michaelmangelsdorf/Sonne8/Prototype/verilog/sasm.c

/* Sonne Microcontroller rev. Myth
    Assembler
  Jan-2024 Michael Mangelsdorf
  Copyr. <mim@ok-schalter.de>
 */

#include <stdio.h>
#include <stdlib.h>
#include <string.h>
#include <ctype.h>

#define LHS_N     0
#define LHS_M     1
#define LHS_D     2
#define LHS_O     3
#define LHS_R     4
#define LHS_I     5
#define LHS_S     6
#define LHS_P     7

#define RHS_G     0
#define RHS_M     1
#define RHS_D     2
#define RHS_O     3
#define RHS_R     4
#define RHS_I     5
#define RHS_S     6
#define RHS_P     7
#define RHS_E     8
#define RHS_X     9
#define RHS_J     10
#define RHS_T     11
#define RHS_F     12
#define RHS_C     13
#define RHS_A     14
#define RHS_B     15

struct myth_vm {

    uint8_t reg_G;
    uint8_t reg_D;
    uint8_t reg_O;
    uint8_t reg_R;
    uint8_t reg_I;
    uint8_t reg_A;
    uint8_t reg_B;
    uint8_t reg_LJO;
    uint8_t reg_C;
    uint8_t reg_L;
    uint8_t reg_E;
    uint8_t reg_SIR;
    uint8_t reg_SOR;
    uint8_t reg_PIR;
    uint8_t reg_POR;
    uint8_t reg_PC;
    uint8_t reg_xMx;

    uint8_t par_ready;
    uint8_t ser_clock;

    uint8_t pagebuf[256];
    uint8_t ram[0x8000];
    
    struct {
        char name[13];
        uint8_t page_idx;
        uint8_t byte_idx;
        uint8_t value;
    } labels;

    void (*E_posedge[16])(struct myth_vm*);
    void (*E_negedge[16])(struct myth_vm*);
} vm;


unsigned pass; /* counts assembly passes */

/* Generate a table of all possible instruction mnemonics */
/* Array index equates to operation code */

char mnemo_decoder[256][12]; /* Various formats */


char *rhs[] = {
"G", "M", "D", "O",
"R", "I", "S", "P",
"E", "X", "J", "T",
"F", "C", "A", "B"
};

void gen_opcodes()
{
    char *lhs[] = {
     "N", "M", "D", "O",
     "R", "I", "S", "P" 
    };

    char *sys[] = {
     "NOP", "SSI", "SSO", "SCL", "SCH", "RDY", "NEW", "OLD",
     "P4", "P1", "P2", "P3", "M4", "M3", "M2", "M1"
    };

    char *aluop[] = {
     "IDA", "IDB", "OCA", "OCB",
     "SLA", "SLB", "SRA", "SRB",
     "AND", "IOR", "EOR", "ADD",
     "CAR", "ALB", "AEB", "AGB"
    };

    char numstr[] = "0";




    // SYS instructions (16 opcodes, 0-15)
    for (int i=0; i<16; i++) {
        strcpy(mnemo_decoder[i], sys[i]);
    }

    // ALU instructions (16 opcodes, 16-31)
    for (int i=16; i<32; i++) {
        strcpy( mnemo_decoder[i], aluop[i-16]);
    }

    // TRAP instructions (32 opcodes, 32-63)
    for (int i=32; i<64; i++) {
        sprintf(mnemo_decoder[i], "*%d", i-32);
    }

    // GETPUT instructions (64 opcodes, 64-127)      
    for (int offs=0; offs<4; offs++)
      for (int regn=0; regn<4; regn++)
        for (int gp=0; gp<2; gp++)
            for (int gl=0; gl<2; gl++)
                {
                    numstr[0] = 48 + offs; // ASCII 0 + the number
                    unsigned index = 64 + regn + 4*gl + 8*gp + 16*offs;
                    if (gp==0) { // GET
                        strcpy( mnemo_decoder[index], gl==0 ? "G" : "L");
                        strcat( mnemo_decoder[index], numstr);
                       switch (regn) {
                        case 0: strcat( mnemo_decoder[index], "a"); break;
                        case 1: strcat( mnemo_decoder[index], "b"); break;
                        case 2: strcat( mnemo_decoder[index], "r"); break;
                        case 3: strcat( mnemo_decoder[index], "i"); break;
                        }
                    }
                    else { // PUT
                       switch (regn) {
                        case 0: strcpy( mnemo_decoder[index], "a"); break;
                        case 1: strcat( mnemo_decoder[index], "b"); break;
                        case 2: strcat( mnemo_decoder[index], "r"); break;
                        case 3: strcat( mnemo_decoder[index], "i"); break;
                        }
                        strcat( mnemo_decoder[index], gl==0 ? "G" : "L");
                        strcat( mnemo_decoder[index], numstr);
                    }
                }


    // PAIR 128-255
    for (int j=0; j<8; j++)
    {
           for (int i=0; i<16; i++)
           {
             /*scrounge*/
           if (j==LHS_N && i==RHS_M) strcpy( mnemo_decoder[j*16+i + 128], "RET");
           else if (j==LHS_D && i==RHS_C) strcpy( mnemo_decoder[j*16+i + 128], "LJO");
           else if(j==LHS_O && i==RHS_C) strcpy( mnemo_decoder[j*16+i + 128], "CPI");
           else if(j==LHS_M && i==RHS_M) strcpy( mnemo_decoder[j*16+i + 128], "CLR");
           else {     
                /* Transfers */
                strcpy( mnemo_decoder[j*16+i + 128], lhs[j] );
//                if (j==RHS_B || j==RHS_BR || j==RHS_BRZ || j==RHS_BT) {
//                    strcat( mnemo_decoder[i*16+j], "'");
//                }
                strcat( mnemo_decoder[j*16+i + 128], rhs[i]);
                //printf("%s %d %d\n", mnemo_decoder[j*16+i], j*16, i);
            }
          }
    }

}




#define SYMSIZE 26

/* Provide a table for frame mnemonics */

char frame_mnemo[256][16][SYMSIZE];
uint8_t frame_refs[256][16];
uint8_t offslabels;
uint8_t frame_lid[256]; /* #Bytes defined in each frame */
uint8_t frame_mnemo_export[256]; /* Non-zero value: export */

uint8_t theDamned;

/* Generate a dictionary for number names */

struct {
    char name[SYMSIZE];
    uint8_t val;
    uint8_t frame;
    int type; // bit map, bit 0=export
} defmap[8192];
unsigned defmap_topindex;

#define BYTE_TO_BINARY_PATTERN "%c%c%c%c_%c%c%c%c"
#define BYTE_TO_BINARY(byte)  \
  (byte & 0x80 ? '1' : '0'), \
  (byte & 0x40 ? '1' : '0'), \
  (byte & 0x20 ? '1' : '0'), \
  (byte & 0x10 ? '1' : '0'), \
  (byte & 0x08 ? '1' : '0'), \
  (byte & 0x04 ? '1' : '0'), \
  (byte & 0x02 ? '1' : '0'), \
  (byte & 0x01 ? '1' : '0') 

#define NYBBLE_TO_BINARY_PATTERN "%c%c%c%c"
#define NYBBLE_TO_BINARY(nybble)  \
  (nybble & 0x08 ? '1' : '0'), \
  (nybble & 0x04 ? '1' : '0'), \
  (nybble & 0x02 ? '1' : '0'), \
  (nybble & 0x01 ? '1' : '0') \

    void create_def( char* label, uint8_t val) {
            sprintf(defmap[defmap_topindex].name, "%s", label);
            defmap[defmap_topindex].val = val;
            defmap_topindex++;
    }

    void populate_defmap()
    {
        defmap_topindex = 0;
        /* Create decimal numbers */
        for (int i=0; i<256; i++) {
            sprintf(defmap[defmap_topindex].name, "%d", i);
            defmap[defmap_topindex].val = i;
            defmap_topindex++;
        }

        /* Create negative decimals */
        for (int i=1; i<=128; i++) {
            sprintf(defmap[defmap_topindex].name, "-%d", i);
            defmap[defmap_topindex].val = -i & 0xFF;
            defmap_topindex++;
        }

        /* Create zero-padded hex numbers */
        for (int i=0; i<256; i++) {
            sprintf(defmap[defmap_topindex].name, "%02X", i);
            strcat(defmap[defmap_topindex].name, "h");
            defmap[defmap_topindex].val = i;
            defmap_topindex++;
        }
        /* Create unpadded hex numbers (nybbles) */
        for (int i=0; i<16; i++) {
            sprintf(defmap[defmap_topindex].name, "%X", i);
            strcat(defmap[defmap_topindex].name, "h");
            defmap[defmap_topindex].val = i;
            defmap_topindex++;
        }
        /* Create binary numbers byte */
        for (int i=0; i<256; i++) {
            sprintf(defmap[defmap_topindex].name, BYTE_TO_BINARY_PATTERN, BYTE_TO_BINARY(i));
            strcat(defmap[defmap_topindex].name, "b");
            defmap[defmap_topindex].val = i;
            defmap_topindex++;
        }
        /* Create binary numbers nybble */
        for (int i=0; i<16; i++) {
            sprintf(defmap[defmap_topindex].name, NYBBLE_TO_BINARY_PATTERN, NYBBLE_TO_BINARY(i));
            strcat(defmap[defmap_topindex].name, "b");
            defmap[defmap_topindex].val = i;
            defmap_topindex++;
        }

        /* Create ASCII names and others */

        create_def("ASCII.backspace", 8);
        create_def("ASCII.linefeed", 10);
        create_def("ASCII.escape", 27);
        create_def("ASCII.space", 32);
        create_def("ASCII.exclamation_mark", 33);
        create_def("ASCII.double_quote", 34);
        create_def("ASCII.hashmark", 35);
        create_def("ASCII.dollar", 36);
        create_def("ASCII.percent", 37);
        create_def("ASCII.ampersand", 38);
        create_def("ASCII.single_quote", 39);
        create_def("ASCII.opening_parenthesis", 40);
        create_def("ASCII.closing_parenthesis", 41);
        create_def("ASCII.asterisk", 42);
        create_def("ASCII.plus_sign", 43);
        create_def("ASCII.comma", 44);
        create_def("ASCII.minus_sign", 45);
        create_def("ASCII.full_stop", 46);
        create_def("ASCII.forward_slash", 47);
        
        // ASCII 0-9 48-57

        create_def("ASCII.colon", 58);
        create_def("ASCII.semicolon", 59);
        create_def("ASCII.less_than_sign", 60);
        create_def("ASCII.equal_sign", 61);
        create_def("ASCII.greater_than_sign", 62);
        create_def("ASCII.question_mark", 63);
        create_def("ASCII.at_sign", 64);

        // ASCII A-Z 65-90

        create_def("ASCII.opening_bracket", 91);
        create_def("ASCII.backward_slash", 92);
        create_def("ASCII.closing_bracket", 93);
        create_def("ASCII.caret", 94);
        create_def("ASCII.underscore", 95);
        create_def("ASCII.back_tick", 96);

        // ASCII a-z 97-122

        create_def("ASCII.opening_brace", 123);
        create_def("ASCII.pipe_symbol", 124);
        create_def("ASCII.closing_brace", 125);
        create_def("ASCII.tilde", 126);
        
        create_def("ASCII.del", 127);

        // Create GLOBAL variable names

        create_def("G0", 128);
        create_def("G1", 129);
        create_def("G2", 130);
        create_def("G3", 131);
        create_def("G4", 132);
        create_def("G5", 133);
        create_def("G6", 134);
        create_def("G7", 135);

        // Create LOCAL variable names

        create_def("L0", 192);
        create_def("L1", 193);
        create_def("L2", 194);
        create_def("L3", 195);
        create_def("L4", 196);
        create_def("L5", 197);
        create_def("L6", 198);
        create_def("L7", 199);


    }




char wordbuf[SYMSIZE];
char tempbuf[SYMSIZE];
char *src; /* Will point to in-memory copy of source file */
long srclength; /* Number of bytes in src file */

/*  Read source file into a memory buffer */

    char* readsrcf( const char* fname)
    {
        FILE* f = fopen( fname,"rb");
        if (!f) return NULL;

        fseek( f, 0, SEEK_END);
        srclength = ftell( f) + 1;
        fseek( f, 0, SEEK_SET);

        char *buffer = malloc (srclength);
        if (buffer) {
          fread (buffer, 1, srclength-1, f);
          buffer[srclength]='\0';
        }
        fclose( f);
        return buffer;
    }

uint8_t isinram = 0;

//uint8_t vm.ram[256*128]; /* 128 (ROM only) frames * 128 bytes = 32k */
unsigned ROM_srcLine[256*128]; /* Which line number generated the output byte */

unsigned objcursor; /* holds current object code byte index */
unsigned objframe; /* hold highest object code frame index */

/* Clear structures */

    void clear()
    {
        for (int i=0; i<(256*128); i++) vm.ram[i] = 0;

        for (int i=0; i<256; i++) 
            strcpy(frame_mnemo[i][offslabels],"");

    }

unsigned cursor; /* holds current source text character index */
unsigned lines; /* tracks number of lines processed */

/* Get a source character relative relative to current position */

    int nextchar( int displacement){
        unsigned index = cursor + displacement;
        if (index < srclength) return src[index];
        else return 0;
    }

/* Move text cursor forward if not outside source buffer */

    int cursor_fwd( int displacement){
    	unsigned index = cursor + displacement;
    	if (index >= srclength) return -1;
    	else cursor = index;
    	return 0;
    }

/* Skip the rest of the current line, including any number of trailing
 * line breaks.
 */

    int skipline(){
    	while (src[cursor]!='\n')
    		if (cursor_fwd(1)) return -1;
    	return 0;
    }

/* Skip any number of space characters */

    int skipspace(){
    	while (src[cursor]==' ' || src[cursor]=='\t')
    		if (cursor_fwd(1)) return -1;
    	return 0;
    }


/* Validate label references */

    int find_backref(char* refstr)
    {
        //printf("BACKW REFSTR=%s\n", refstr);
        unsigned here;
            here = objframe;
            for (int i=here; i>=0; i--) {
                for(int j=0; j<16; j++)
                    if (!strcmp(refstr, frame_mnemo[i][j])) {
                        theDamned = i;
                        return frame_refs[i][j];
                    }
            }
        return -1;
    }

    int find_fwdref(char* refstr)
    {
        //printf("FWD REFSTR=%s\n", refstr);
        unsigned here;
            here = objframe;
            for (int i=here; i<256; i++) {
                for(int j=0; j<16; j++) {
                    //if (!strcmp(refstr, "skip") && i<4)
                    //    printf("i=%d, j=%d, %s, searching for:%s %d\n", i,j, frame_mnemo[i][j], refstr, frame_refs[i][j]);
                    if (!strcmp(refstr, frame_mnemo[i][j])) {
                        theDamned = i;
                        return frame_refs[i][j];
                    }
                }
            }
        return -1;
    }

    int find_mcref(char* refstr)
    {
        //printf("FWD REFSTR=%s\n", refstr);
        unsigned here;
        for (int i=0; i<256; i++)
            for(int j=0; j<16; j++)
                if (!strcmp(refstr, frame_mnemo[i][j])) return i;
        return -1;
    }




/* Try to find the frame and the type of a defmap entry */

    int defmap_frame_and_type(char* buf, uint8_t* typefound)
    {
        for (int i=0; i<defmap_topindex; i++)
        {
            if (!strcmp( defmap[i].name, buf)) {
                //printf ("Found def %s\n", wordbuf);
                *typefound = defmap[i].type;
                return defmap[i].frame;
            }
        }
        return -1;
    }

/* Try to find an entry matching wordbuf in precompiled mnemonics */

    int compare_to_tables(char* buf)
    {
        for (int i=0; i<256; i++)
        {
            if (!strcmp( mnemo_decoder[i], buf)) {
                //printf ("Found mnemonic %s (%02X)\n", wordbuf, i);
                return i;
            }
        }

        for (int i=0; i<defmap_topindex; i++)
        {
            if (!strcmp( defmap[i].name, buf)) {
                //printf ("Found def (or number literal!) %s\n", buf);
                return defmap[i].val;
            }
        }
        return -1;
    }


/* Store an object code byte and move on */

    void store( uint8_t byte)
    {
            ROM_srcLine[objframe * 128 + objcursor] = lines;
            vm.ram[objframe * 128 + objcursor] = byte;
            frame_lid[objframe]++;

        if (++objcursor > 127) {
            printf("Code frame overflow in line %d\n", lines);
            exit(0);
        }
    }


int labelallowed; /* Only one frame label per full-stop */
int endframe;
int handled;
int ramgap;


void
check_if_ref(char* mybuf)
{
    int k;
     if (mybuf[0]=='<') {
        if (strlen(mybuf)<2) {
            printf("Empty back reference, line %d\n** ERROR **\n", lines);
            exit(0);
        }
        k = find_backref(mybuf+1);
        if (theDamned == objframe && k>=objcursor) k=-1; //Handle offset labels
        handled = 1;
    }
    if (mybuf[0]=='>') {
        if (strlen(wordbuf)<2) {
            printf("Empty forward reference, line %d\n** ERROR **\n", lines);
            exit(0);
        }
        k = find_fwdref(mybuf+1);
        if (theDamned == objframe && k<objcursor) k=-1; //Handle offset labels
        //printf("searching for >%s\n",wordbuf+1);
        handled = 1;
    }
    if (handled && k == -1) {
        if (pass==2) {
            printf("Unresolved reference '%s', line %d\n** ERROR **\n", mybuf, lines);
            exit(0);
        }
    }
    if (handled) {
         store(isinram ? k+128 : k);
         //printf("k was %d for %s\n", k, wordbuf);   
    }
}


/* We assert that this is called when cursor is at the first character
 * of a new line, following a line break character.
 * Assemble this line.
 */

    int beginline()
    {
        uint8_t opc_colon;
    	lines++;
        if (src[cursor] == '\n') {
            if (cursor_fwd(1)) return 0; /* skip empty lines */
            else return -1;
        }
        while (skipspace() == 0)  /* Skip leading white space */
        {
            endframe = 0;
            /* We assume that the current word does not end with full-stop */

            handled = 0; /* We haven't handled this word so far */

            /* We are now positioned at the first character of something */
            /* What is it? */

            if (src[cursor] == '\n') { /* It's a newline character, skip it */
                if (cursor_fwd(1)) return 0;
                else return 1; /* Enter next line */
            }
        	
            if (src[cursor] == ';') { /* Beginning of a comment, skip it */
        		if (skipline()) return 0;
                if (cursor_fwd(1)) return 0; /* Skip the newline character */
                else return 1; /* Enter next line */
            }

            /* It's something non-trivial, copy it into the word buffer */
            int k=0;
            while (nextchar(k)!=' ' && nextchar(k)!='\t' && nextchar(k)!='\n')
            {
                wordbuf[k] = nextchar(k);
                if (cursor + k >= srclength) {
                    printf("Unexpected end of file\n");
                    exit(0);
                }
                if (k++ > 79) {
                    printf("Buffer overrun - string literal too long\n");
                    exit(0);
                }
            }
            wordbuf[k] = 0; /* Force null termination */

            if (k>0 && wordbuf[0] == '"') {
                printf("String %s\n", wordbuf);
                // Compile string
                for (int i=1; i<k; i++) {
                    printf("%c ", wordbuf[i]);
                    store(wordbuf[i]);
                }
                printf("\n");
                handled=1;
            }


            if (k>0 && wordbuf[k-1]==',' && wordbuf[0] != '"') wordbuf[k-1]='\0'; /* Ignore commas */
            else
            if (k>0 && wordbuf[k-1]=='.' && wordbuf[0] != '"') {
                wordbuf[k-1]='\0'; /* Strip the full-stop */
                //endframe = 1;
            }

            /* The word is now a zero terminated string in wordbuf */
            /* Now check what we got there... */

            /* First of all, is it short enough to be managed as a symbol? */
            if (strlen(wordbuf)>=SYMSIZE) {
                printf("Max. symbol length exceeded for '%s', line %d\n", wordbuf, lines);
                exit(0);
            }

            if (!strcmp(wordbuf,"RAM")) {
                printf("-RAM-\n");
                //ramgap = objcursor ? objframe : objframe -1;
                //objframe = 128;
                //objcursor = 0;
                handled = 1;
                labelallowed = 1;
                handled = 1;
                isinram = 1;
            }
            

            /* Check for offset label definition */
            if (!handled && strlen(wordbuf)>1) {
                int endpos = strlen(wordbuf)-1;
                if (wordbuf[endpos]=='@' && wordbuf[0] != '"') {
                    wordbuf[endpos] = '\0';
                    /* ! prefix means export this symbol, don't throw away */
                    /* pass ==2 avoid duplicate export symbols */
                    if (wordbuf[0]=='!' && pass==2) {
                    }
                    else frame_mnemo_export[objframe] = 0;
                    strcpy(frame_mnemo[objframe][offslabels], wordbuf);
                    frame_refs[objframe][offslabels] = objcursor;
                    //printf("Defining %s@ objframe=%d offslabels=%d offs:%d\n", wordbuf, objframe, offslabels, objcursor);
                    offslabels++;
                    handled = 1;
                }
            }

            /* Check for offset label #frame reference */
            if (!handled && strlen(wordbuf) && wordbuf[0]=='#') {
                uint8_t type;
                k = defmap_frame_and_type( wordbuf+1, &type);
                if (k != -1) {
                    store(k);
                    handled = 1;
                }
            }


            // Implement 45h:N, >LBL:J etc.
            if (!handled)
            {
                int found = 0;
                char lbuf[40];
                char rbuf[40];
                for (int i=0; i<strlen(wordbuf); i++) {
                    if (wordbuf[i]==':') { found=i; break; };
                }
                if (found) {
                    for (int i=0; i<40; i++) lbuf[i] = rbuf[i] = 0;
                    for (int i=0; i<found; i++) lbuf[i] = wordbuf[i];
                    for (int i=found+1; i<strlen(wordbuf); i++) rbuf[i-found-1] = wordbuf[i];
                    //printf("%s : %s\n", lbuf, rbuf);
                            // Opcode is Nx! = 80h + rhs[]
                            opc_colon = 0;
                            for (int i=0; i<16; i++)
                                if (!strcmp(rbuf, rhs[i])){
                                   opc_colon = 0x80 + i;
                                   break;
                                }
                    //printf("opcode = %02X\n", opc_colon);
                    if (!opc_colon) { printf("Invalid : expression %s, line %d\n", wordbuf, lines); exit(1); }
                    store(opc_colon);

                    //Now find literal value using lbuf
                    //Number hex dec bin
                    //Ref fwd, back
                    /* Check precompiled tables of mnemonics and number literals */
                    k = compare_to_tables(lbuf);
                    if (k != -1) {
                        store(k);
                        handled = 1;
                    }
                    else check_if_ref(lbuf);
                }
            }



            /* Check for frame label definition */
            if (wordbuf[0]=='@') {
                if (!handled && labelallowed)
                { /* Check if it's a frame label definition @LABEL */
                        if (strlen(wordbuf)<2) {
                            printf("Empty label definition, line %d\n", lines);
                            exit(0);
                        }

                        if (objcursor) {
                           printf("Label definition in anonymous frame, line %d\n** ERROR **\n", lines);
                           exit(0);
                        }

                        int endpos = strlen(wordbuf)-1;
                        if (wordbuf[endpos]=='!'  && wordbuf[0] != '"') {
                                wordbuf[endpos] = '\0';
                                frame_mnemo_export[objframe] = 1;
                                //printf("Found export label: %s\n", wordbuf);
                        }
                        else frame_mnemo_export[objframe] = 0;
                        strcpy(frame_mnemo[objframe][offslabels], wordbuf+1);
                        frame_refs[objframe][offslabels] = objframe;
                        //printf("Defining @%s objframe=%d offslabels=%d\n", wordbuf+1, objframe, offslabels);
                        offslabels++;
                        labelallowed = 0; /* only 1 frame label per full stop */
                        handled = 1;
                }
                if (!handled)
                {
                    printf("Duplicate frame label %s, line %d\n** ERROR **\n", wordbuf, lines);
                    exit(0);
                }
            }

            if (!handled) /* Check if it's a label reference <LABEL or >LABEL */
            {
               check_if_ref(wordbuf);
            }





            if (!handled) {
                /* Check precompiled tables of mnemonics and number literals */
                k = compare_to_tables(wordbuf);
                if (k != -1) {
                    store(k);
                    handled = 1;
                }
            }

            if (!handled) {
                /* See if it contains an equal sign (a DEF) */
                char *p = strstr(wordbuf,"=");
                char *p_equalsign = p;
                if (p) {
                    p++;
                    k = 0;
                    do tempbuf[k++] = *p; while (*(p++) != '\0');
                    
                    /* tempbuf now holds the thing that the DEFined label */
                    /* is supposed to equate to */
                    /* Look it up to see if we know what they mean */
                    k = compare_to_tables(tempbuf);
                    if (k == -1)
                    {
                        printf("Unknown assignment value: %s, line %d\n** ERROR **\n", tempbuf, lines);
                        exit(0);
                    }
                    /* OBliterate the = character in wordbuf to leave only DEF label */
                    *p_equalsign = '\0';

                    if (compare_to_tables(wordbuf) != -1) {
                            printf("WARNING: Label definition %s redefines previous!\n", wordbuf);
                    }

                    /* ! prefix means export this symbol, don't throw away */
                    /* pass ==1 avoid duplicate export symbols */
                    if (pass==1){
                        if (wordbuf[0]=='!') {
                            defmap[defmap_topindex].type |= 1;
                            /* Skip ! */
                            strcpy( defmap[defmap_topindex].name, wordbuf+1 );
                        }
                        else strcpy(defmap[defmap_topindex].name, wordbuf);
                        defmap[defmap_topindex++].val = k;
                    }        
                    handled = 1;
                }
            }

            if (!handled) {
                if (wordbuf[0]=='*') {
                    if (strlen(wordbuf)<3) {
                        printf("Empty micro-call reference, line %d\n** ERROR **\n", lines);
                        exit(0);
                    }
                    /* Check if it's a micro-call */
                    k = find_mcref(wordbuf+1);
                    if (k != -1) {
                        handled = 1;
                        store(k | 0x20);
                        //store(k); // Fling is gone
                    } else {
                        if (pass==2) {
                            printf("Unresolved micro-call reference '%s', line %d\n** ERROR **\n", wordbuf, lines);
                            exit(0);
                        }
                    }
                }
            }

            if (!handled) {
                if (wordbuf[0]=='"') {
                    if (strlen(wordbuf)<2) {
                        printf("Empty string literal, line %d\n** ERROR **\n", lines);
                        exit(0);
                    }
                    for (k=1; k<strlen(wordbuf); k++) store(wordbuf[k]);
                    handled = 1;
                }
            }

            if (!handled && !strcmp(wordbuf,"CLOSE")) handled=1;


            // Handle special case for Nx : '3R', '22h' etc.
            if (!handled && isdigit(wordbuf[0])) {
                    // Opcode is Nx! = 80h + rhs[]
                    opc_colon = 0;
                    for (int i=0; i<16; i++)
                        if (!strcmp(wordbuf + strlen(wordbuf)-1, rhs[i])){
                           opc_colon = 0x80 + i;
                           break;
                        }

                    wordbuf[strlen(wordbuf)-1]=0; //Chop dst register
                    k = compare_to_tables(wordbuf);
                    if (k != -1 && opc_colon) {
                        store(opc_colon);
                        store(k);
                        handled=1;
                    }
            }


            if (!handled && pass==2)
            //if (!handled && pass==2)
            {
               printf("Unknown symbol: %s, line %d\n", wordbuf, lines);
               exit(1);
            }
            

            /*  -- Below only finishing up with the current word -- */

            /* Any full-stop closes the frame AFTER handling the preceding word
               Full-stop is an alias for LID, RET also closes the frame
             */
            if (endframe || !strcmp(wordbuf,"CLOSE"))
            {
                    if (objframe+1 > 255){
                        printf("Frame index overflow in line %d\n** ERROR **\n", lines);
                        exit(0);
                    }

                if (endframe) store(RHS_M * 16 + LHS_M); // LID opcode
                
                if (endframe || !strcmp(wordbuf,"CLOSE"))
                objframe++;
                objcursor = 0;
                labelallowed = 1;
                endframe = 0;
                offslabels = 0;
            }

            /* Skip over it, watch out it may be followed by newline */
            while (src[cursor]!=' ' && src[cursor]!='\t')
            {
                if (src[cursor]=='\n') {
                    if (cursor_fwd(1)) return 0; /* End of line */
                    else return -1;
                }
                else if (cursor_fwd(1)) return 0;
            }
            /* Try the next word */
        }
        return 0;
    }

void
mifgen( char *fname)
{
    FILE *f;
    int i;
    f = fopen( fname, "wb");
    if (f) {
        fprintf( f, "-- MCBastard output image\n\n");
        fprintf( f, "DEPTH = %d;\n", 0x8000);
        fprintf( f, "WIDTH = 8;\n");
        fprintf( f, "ADDRESS_RADIX = HEX;\n");
        fprintf( f, "DATA_RADIX = HEX;\n");
        fprintf( f, "CONTENT\n");
        fprintf( f, "BEGIN\n\n");

        for (i = 0; i<256*128; i++) {
            fprintf( f, "%04X : %02X;\n", i, vm.ram[ i]);
        }

        fprintf( f, "\nEND;\n");
        fclose( f);
    }
}

char* tobin( int i, char* mynum){
    mynum[0] = i&128 ? '1' : '0';
    mynum[1] = i&64 ? '1' : '0';
    mynum[2] = ' ';
    mynum[3] = i&32 ? '1' : '0';
    mynum[4] = i&16 ? '1' : '0';
    mynum[5] = i&8 ? '1' : '0';
    mynum[6] = ' ';
    mynum[7] = i&4 ? '1' : '0';
    mynum[8] = i&2 ? '1' : '0';
    mynum[9] = i&1 ? '1' : '0'; 
    mynum[10] = 0;
    return mynum;
}

void byteToBinaryString(unsigned char byte, char binaryString[9]) {
    int i;
    for (i = 7; i >= 0; i--) {
        binaryString[7 - i] = ((byte >> i) & 1) ? '1' : '0';
    }
    binaryString[8] = '\0';
}

int main (int argc, char **argv)
{

    char* mynum[11];
    printf("\n/* Sonne Microcontroller rev. Myth\n");
    printf("   Assembler");
    printf("  Jan-2024 Michael Mangelsdorf\n");
    printf("  Copyr. <mim@ok-schalter.de>\n");
    printf("*/\n\n");

    char* fname;
    if (argc<2){
        fname = "myth.asm";;
        printf("Missing work file name, using default '%s'\n", fname);
        //exit(-1);
    } else fname = argv[1];

	src = readsrcf( fname);
    if (!src) {
        printf("Requires input file '%s'\n\n", fname);
        
        exit(0);
    }
    srclength--;
	printf("%ld bytes read\n", srclength);

	clear();
    pass = 0;


    populate_defmap(); //for (int i=0; i<defmap_topindex; i++) printf("%s %d\n", defmap[i].name, defmap[i].val);

    gen_opcodes(); //for (int i=0; i<128; i++) printf("%s\n", mnemo_decoder[i]);
    FILE *f = fopen("opcode_matrix.txt","w");
    fprintf(f,"\n     LSB ");
    for (int i=0; i<16; i++) fprintf(f, NYBBLE_TO_BINARY_PATTERN " ", NYBBLE_TO_BINARY(i));
    fprintf(f,"\n\n         ");
    for (int i=0; i<16; i++) fprintf(f,"%-4X ",i);
    fprintf(f,"\nMSB      ");
    for (int i=0; i<16; i++) fprintf(f,"---- ");
    fprintf(f,"\n");
    for (int i=0; i<16; i++) {
        if (i==1 || i==2 || i==4 || i==8) fprintf(f,"\n");
        fprintf(f, NYBBLE_TO_BINARY_PATTERN " " "%X_  ", NYBBLE_TO_BINARY(i), i);
        for (int j=0; j<16; j++) {
                        fprintf(f, "%-4s ", mnemo_decoder[i*16+j]);
        }
        fprintf(f,"\n");
    }

////localparam opc_NOP = 8'h00;
    fprintf(f,"\n\n\n\n");
    char mystr[6];
    for (int i=0; i<256; i++) {
                for (int j=0; j<6;j++) mystr[j]=0;
                for (int j=0;j<strlen(mnemo_decoder[i]); j++) mystr[j]=toupper(mnemo_decoder[i][j]);
                fprintf(f,"localparam opc_%-3s = 8'h%02X;\n",  mystr, i);
    }

//    fprintf(f,"\n\n\n\n");
//    for (int i=0; i<256; i++) {
//                fprintf(f,"%02X %s\n",i, mnemo_decoder[i]);
//    }



    fprintf(f,"\n\n\n\n");

    fprintf(f,"const char *opcodes[256] = {\n");
    for (int i=0; i<32; i++) {
        for (int j=0; j<8; j++) {
            fprintf(f,"\"%s\"", mnemo_decoder[i*8+j]);
            if (i==31 && j==7) break;
            else fprintf(f,", ");
        }
        if (i!=31) fprintf(f, "\n");
    }
    fprintf(f,"\n};\n\n");

    fprintf(f,"#define NUMBERS_ARRAY_SIZE 928\n");
    fprintf(f,"struct {char *name; uint8_t val;} numbers[NUMBERS_ARRAY_SIZE] = {\n");
    for (int i=0; i<928/4; i++){
        for (int j=0; j<4; j++) {
            fprintf(f,"{\"%s\",0x%02X}", defmap[i*4+j].name, defmap[i*4+j].val);
            if (i==(928/4)-1 && j==3) break;
            else fprintf(f,", ");
        }
        if (i!=928/4-1) fprintf(f,"\n");
    }
    fprintf(f,"\n};\n\n");

    fclose(f);


    for (pass=1; pass<3; pass++) {
        printf("Pass %d\n", pass);

        for (int i=0; i<256; i++) frame_lid[i] = 0;
        for (int i=0; i<256; i++) ROM_srcLine[i] = 0;

        ramgap = -1;
        cursor = 0;
        objcursor = 0;
        objframe = 0;
        lines=0;
        labelallowed=1;
        offslabels=0;
    	while (beginline()); /* Traverse source-text by lines */
    }

	    printf("%d lines processed\n", lines);

        /* Write the lid values into pos 7Fh of each frame.
         This convention serves to make use of the usually large
        proportion of unused space after the initial train of code.
        The lid value at a fixed location provides the offset of
        the first unused byte in each frame. */

        for (int i=0; i<256; i++) {
            vm.ram[ 128*i + 0x7F ] = frame_lid[i]; 
        }

        /* Generate exported symbols table */
        #define BIG 16*1024
        char symtab[BIG];
        memset( symtab, 0, BIG);

        /* Format symbols as: STRING SPACE BYTE <NEXT STRING> */
        unsigned symtab_index = 0;


        symtab[symtab_index++] = '\0'; // Instructions
        symtab[symtab_index++] = 1;
        for (int i=0; i<256; i++) {
            sprintf(tempbuf, "%s %c", mnemo_decoder[i], i);
            for (int j=0; j<strlen(mnemo_decoder[i])+2; j++) symtab[symtab_index++] = tempbuf[j];
        }

        symtab[symtab_index++] = '\0'; // Frame labels
        symtab[symtab_index++] = 3;
        for (int i=0; i<objframe; i++)
            if (frame_mnemo_export[i]) {
                 sprintf(tempbuf, "%s %c", frame_mnemo[i][offslabels], i);
                for (int j=0; j<strlen(frame_mnemo[i][offslabels])+2; j++) symtab[symtab_index++] = tempbuf[j];
            }

        symtab[symtab_index++] = '\0'; // Definitions
        symtab[symtab_index++] = 4;
        for (int i=0; i<defmap_topindex; i++) {
            if (strlen(symtab)>=BIG) {
                printf("Exported symbols table exceeds 16k limit!\n");
                exit(0);
            }
            if (defmap[i].type & 1) {
                sprintf(tempbuf, "%s %c", defmap[i].name, defmap[i].val); 
                for (int j=0; j<strlen(defmap[i].name) +2; j++) {
                    symtab[symtab_index++] = tempbuf[j];
                }
            }
        }

        printf("Export symbols table: %d bytes\n", symtab_index);
        printf("\n");

        /* Cram exported symbols table into unused gap in object file */
        /* Use the lid values of each frame for this. */
        /* Space from offset "lid" to offset 7Fh of each frame is empty! */

        uint8_t offs;
        uint8_t val, tablecode=0;
        unsigned max_index = symtab_index;
        symtab_index = 0;
        int i;
//        for (i=0; i<128; i++) {
//            offs =  vm.ram[128*i + 0x7F]; /* Set offs to frame lid */
//            if (offs==0x7F) {
//                 printf("Full frame error - lid convention!\n");
//                 exit(0);
//            }
//            while (offs < 0x7F) {
//                val = symtab[symtab_index++];
//                vm.ram[128*i + offs++] = val;
//                if (symtab_index == max_index) break;
//            }
//            if (symtab_index == max_index) break;
//        }


    printf("Writing object file...\n\n");

    f = fopen("myth.obj","w");
    fwrite(&vm, 1,
        sizeof(struct myth_vm)
         - 2 * sizeof(void (*[16])(void)),
    f);
    fclose(f);

    mifgen("myth.mif"); // MIF file for Quartus import

      /* Output a concordance for debugging */

    f = fopen("debug.txt","w");

    fprintf(f, "\nAssembly output (pass 2)\n");
    fprintf(f, "\nSuppressing output of embedded export symbols!\n\n");
    //fprintf(f, "Frame.Offset      Object Code       Line#  Source text\n\n");
    fprintf(f, "Frame.Offset     Object Code        Lid Line#  Source text\n\n");
    int k = 0;
    lines = 1;
    int outputlen;
    int lead_frame=0, lead_offset=0;

    while (k<srclength) {

        /* Write object code generated for line*/

        lead_frame = -1;
        lead_offset = -1;
        for (int frame=0; frame<=objframe; frame++)
            for (int offset=0; offset<128; offset++)
                if (ROM_srcLine[frame*128 + offset] == lines) {
                    if (lead_frame == -1) lead_frame = frame;
                    if (lead_offset == -1) lead_offset = offset;
                }

        if (lead_frame != -1 || lead_offset != -1)
        {
            fprintf(f, "%02X.%02X:  ", lead_frame, lead_offset);
        }
        else fprintf(f, "        ");

        outputlen = 0;
        int linefill = 0;
        for (int frame=0; frame<=objframe; frame++) {
            for (int offset=0; offset<128; offset++) {
                if (ROM_srcLine[frame*128 + offset] == lines) {
                    if (!(++linefill%8)) {
                        fprintf(f, "\n        ");
                        outputlen -= 21;
                    }
                    lead_frame = frame;
                    lead_offset = offset;
                    fprintf(f, "%02X ", vm.ram[frame*128+offset]);
                    outputlen += 3;
                    if (offset>frame_lid[frame]) break;
                }
            }
        }

        if (outputlen) outputlen = outputlen>(24+3) ? 24 : outputlen-3;
        else outputlen = -3;

        /* pad missing hex output */
        for (int i=(24-outputlen); i>0; i--) fprintf(f, " ");
        if ( lead_frame != -1 && frame_lid[lead_frame])
            fprintf(f, " %3d %04d  ", frame_lid[lead_frame], lines);
        else
            fprintf(f, "     %04d  ", lines);

        while (k<srclength && src[k++] != '\n')
        {
            fprintf(f, "%c", src[k-1]);
        }
        lines++;
        fprintf(f, "\n");
    }

    fclose(f);

}
